fyafighter/shotbot/drawings/v2/base1.dxf

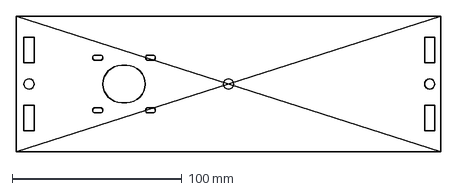
[picture p15: CAD file, 2020-08-28]
drawings/v2/base1.dxf
250.0 x 80.0 mm
