fyafighter/shotbot/drawings/v2/pan-axis-spacer-30mm.dxf

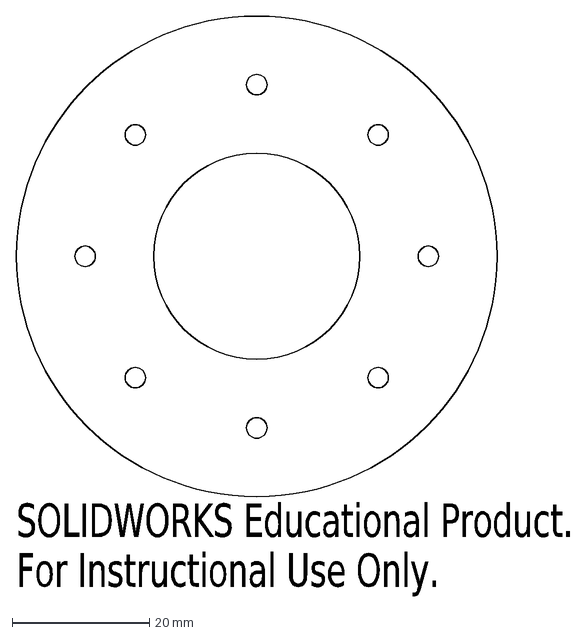
[picture p16: CAD file, 2020-08-28]
drawings/v2/pan-axis-spacer-30mm.dxf
SOLIDWORKS Educational Product.
For Instructional Use Only.
