fyafighter/shotbot/drawings/v2/XL-timing-pulleys.dxf

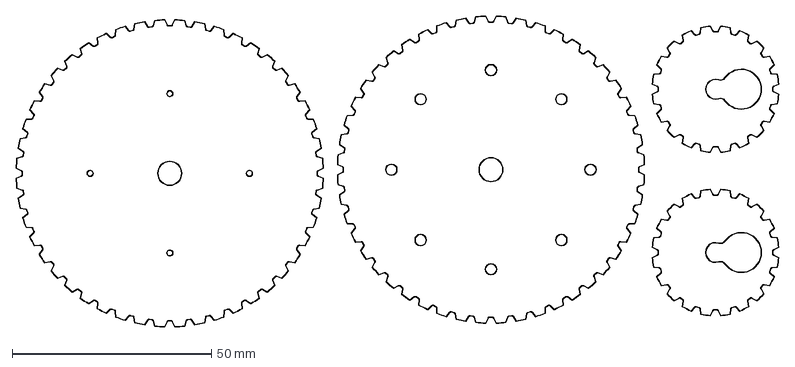
[picture p17: CAD file, 2020-08-28]
drawings/v2/XL-timing-pulleys.dxf
191.4 x 78.0 mm
