fyafighter/shotbot/drawings/v2/pan-tray.stl

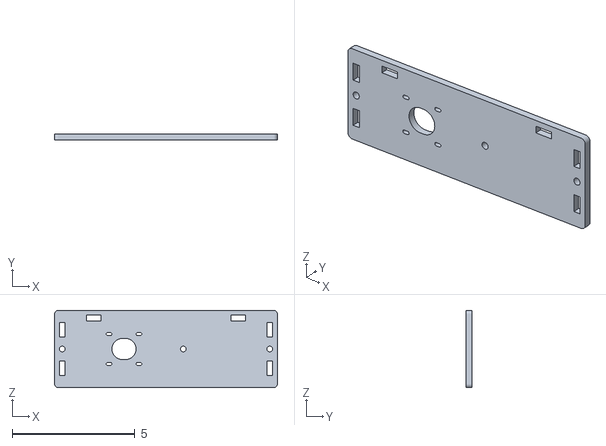
[picture p18: CAD file, 2020-08-28]
drawings/v2/pan-tray.stl
9.09 x 0.236 x 3.15
