fyafighter/shotbot/drawings/v2/pan-tray-flange-no-motor.dxf

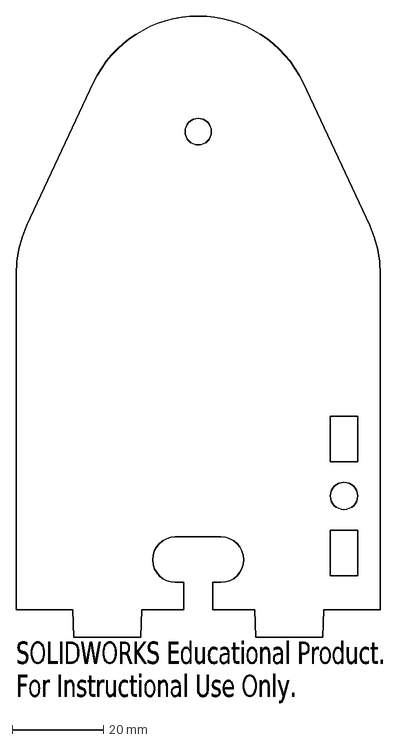
[picture p19: CAD file, 2020-08-28]
drawings/v2/pan-tray-flange-no-motor.dxf
SOLIDWORKS Educational Product.
For Instructional Use Only.
