fyafighter/shotbot/drawings/v2/pan-base.stl

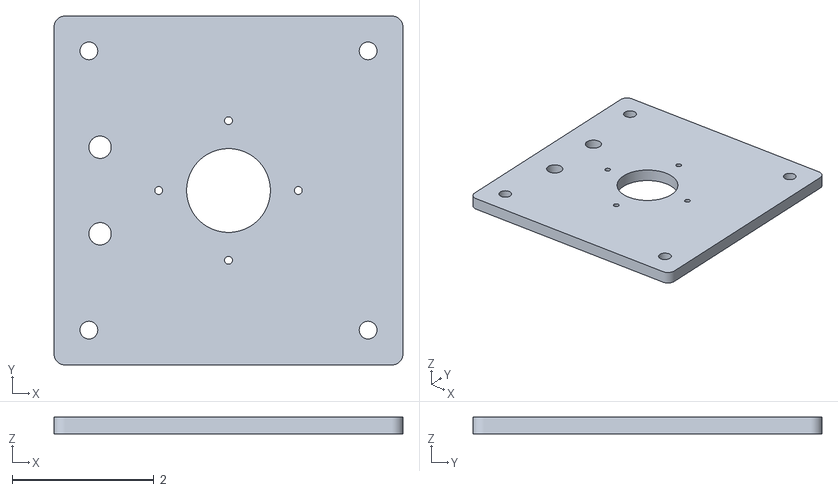
[picture p20: CAD file, 2020-08-28]
drawings/v2/pan-base.stl
4.92 x 4.92 x 0.236
