fyafighter/shotbot/drawings/v2/tilt-tray.stl

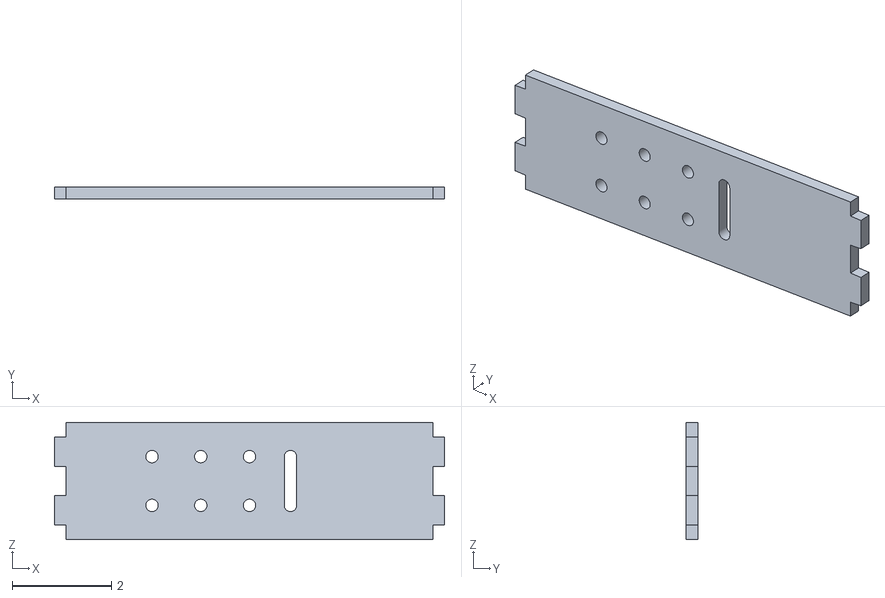
[picture p21: CAD file, 2020-08-28]
drawings/v2/tilt-tray.stl
7.87 x 0.236 x 2.36
