fyafighter/shotbot/drawings/v2/pan-XL-timing-pulley.stl

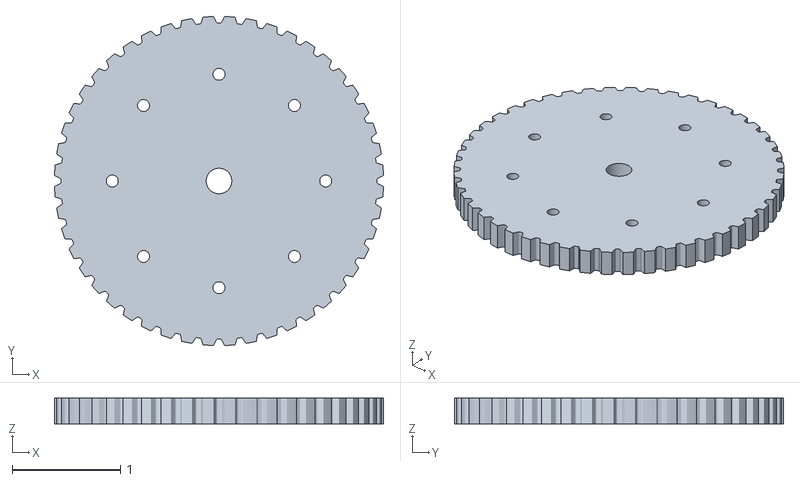
[picture p22: CAD file, 2020-08-28]
drawings/v2/pan-XL-timing-pulley.stl
3.03 x 3.03 x 0.236
