fyafighter/shotbot/drawings/v2/pan-axis-spacer.stl

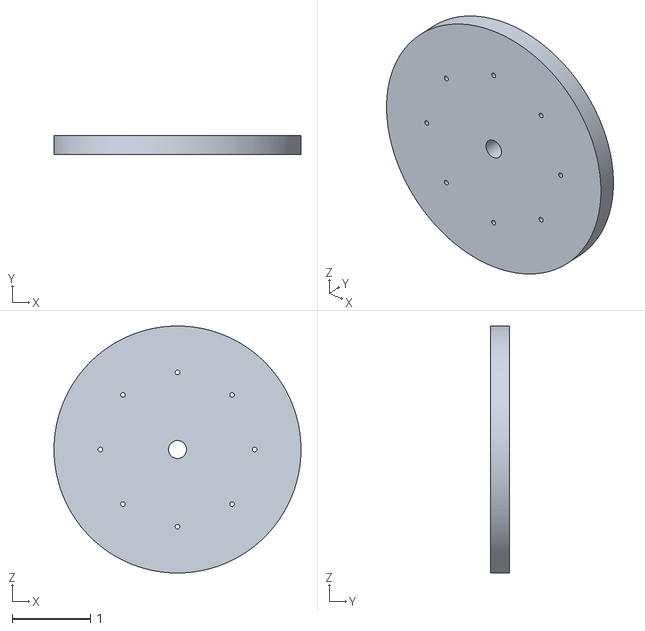
[picture p23: CAD file, 2020-08-28]
drawings/v2/pan-axis-spacer.stl
3.15 x 0.236 x 3.15
