fyafighter/shotbot/drawings/v2/pan-tray-flange-with-stepper.dxf

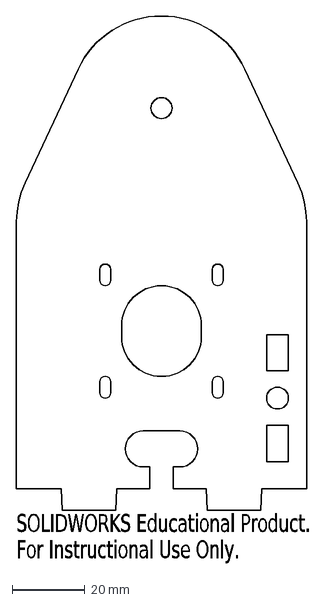
[picture p24: CAD file, 2020-08-28]
drawings/v2/pan-tray-flange-with-stepper.dxf
SOLIDWORKS Educational Product.
For Instructional Use Only.
